HabonRoof/nixietube_clock/doc/picture/tap_inductor/IR/FLIR0199.jpg

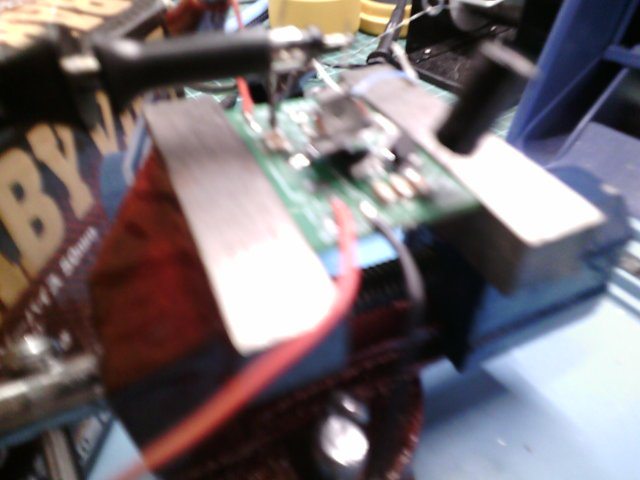
doc/picture/tap_inductor/IR/FLIR0199.jpg
