HabonRoof/nixietube_clock/doc/datasheet/divergence_meter_eevblog.gif

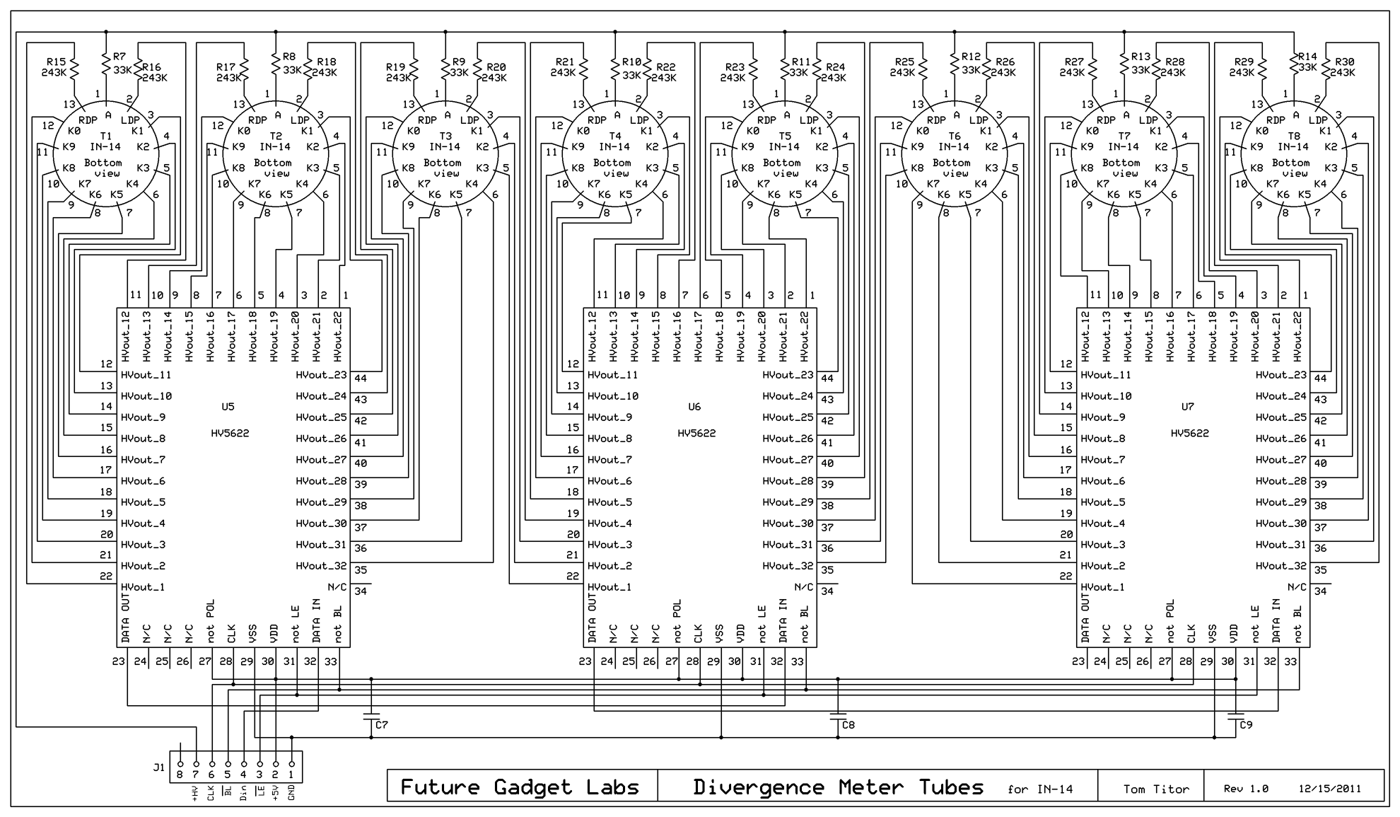
doc/datasheet/divergence_meter_eevblog.gif
