HabonRoof/nixietube_clock/doc/picture/single_board/IR/10mA_1.jpg

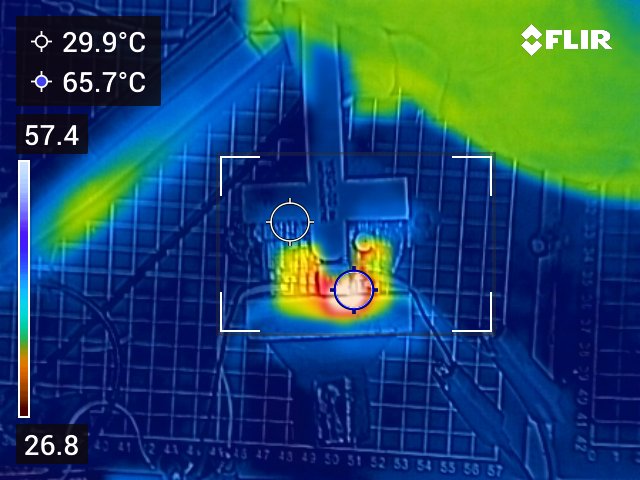
doc/picture/single_board/IR/10mA_1.jpg
