HabonRoof/nixietube_clock/doc/picture/single_board/IR/10mA_3.jpg

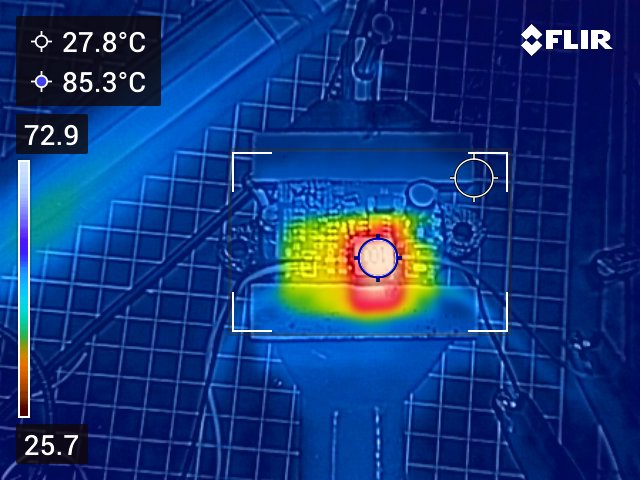
doc/picture/single_board/IR/10mA_3.jpg
