HabonRoof/nixietube_clock/doc/picture/single_board/waveform/0A175V000.png

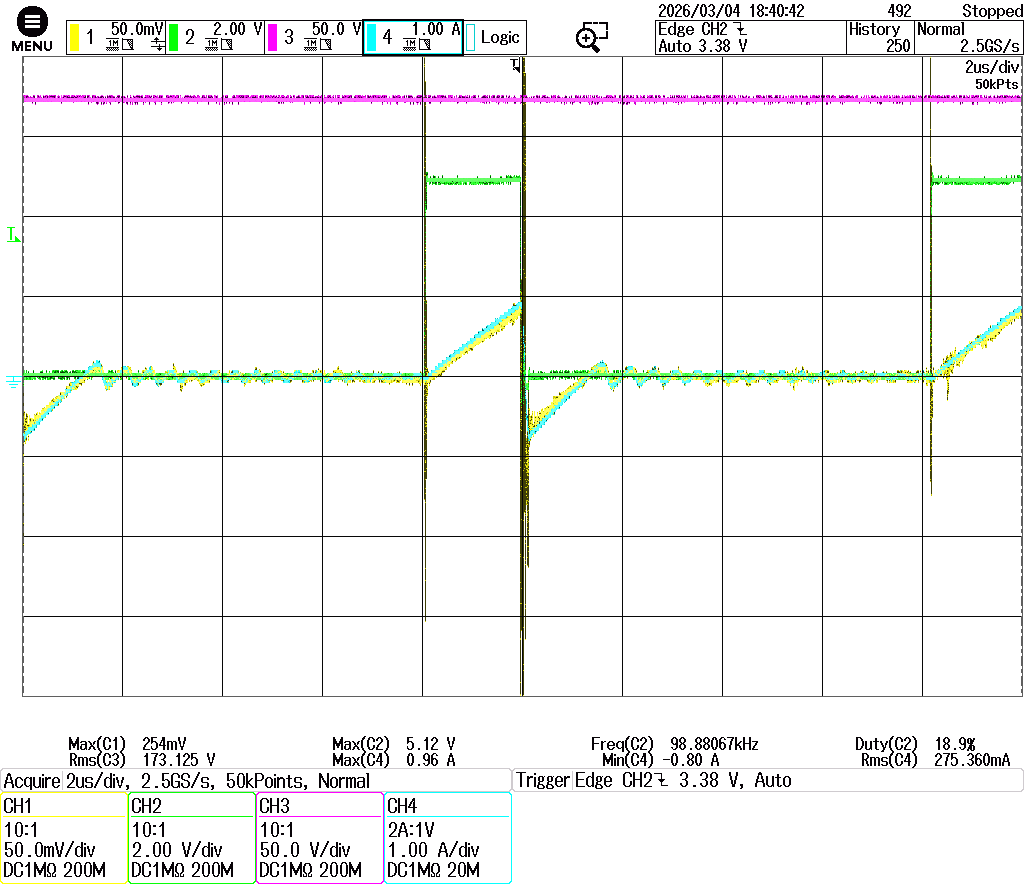
doc/picture/single_board/waveform/0A175V000.png
