HabonRoof/nixietube_clock/doc/picture/single_board/waveform/5vin_160vout_0Aout.png

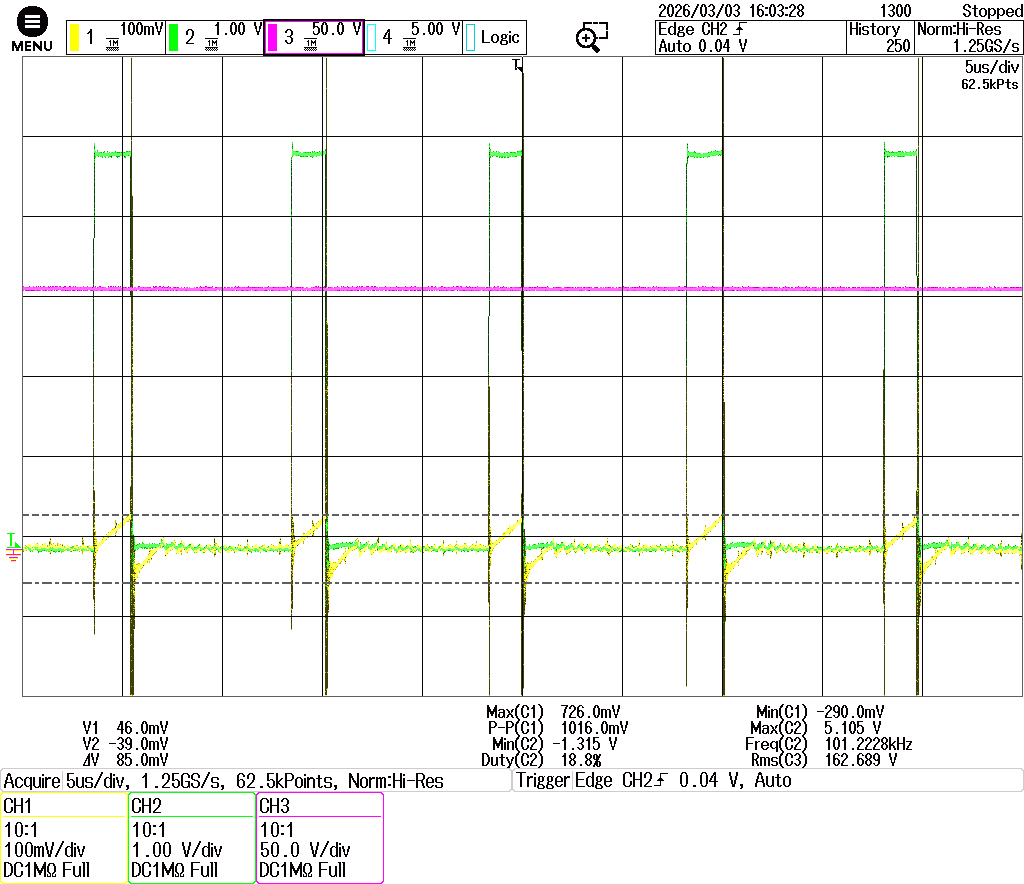
doc/picture/single_board/waveform/5vin_160vout_0Aout.png
