HabonRoof/nixietube_clock/doc/picture/single_board/waveform/5vin_160vout_5mAout.png

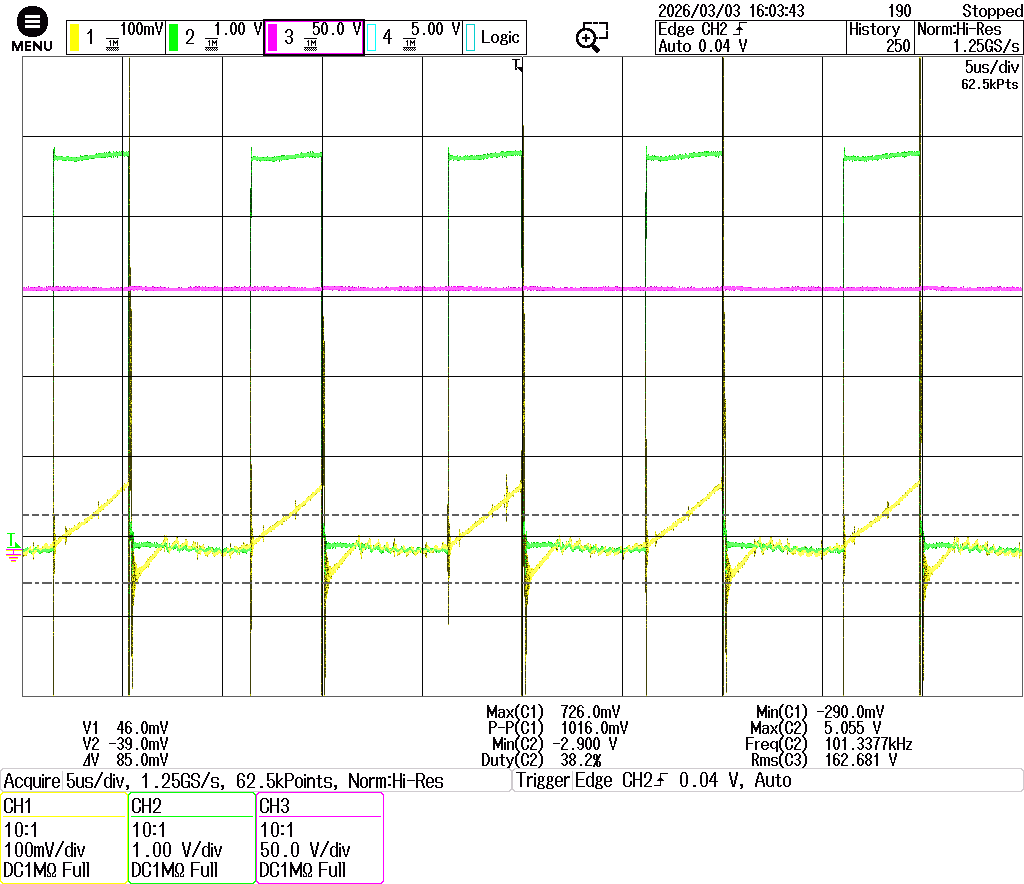
doc/picture/single_board/waveform/5vin_160vout_5mAout.png
