HabonRoof/nixietube_clock/doc/picture/single_board/waveform/8mA175V000.png

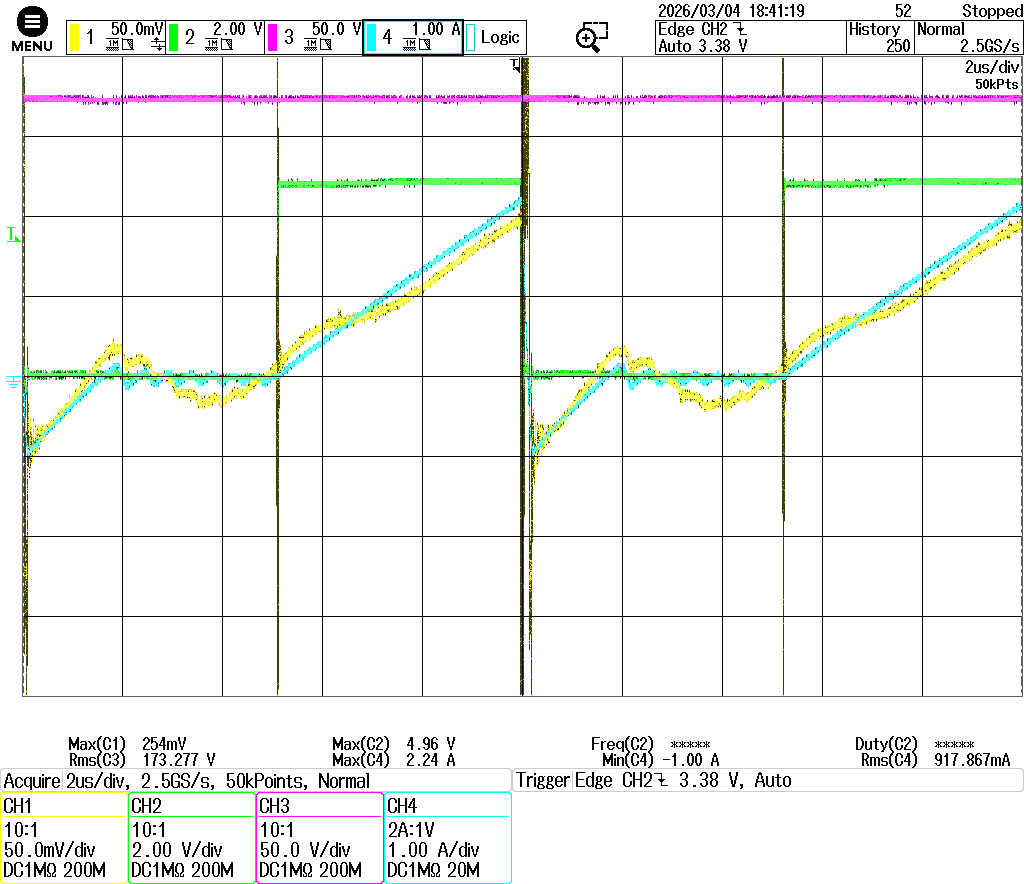
doc/picture/single_board/waveform/8mA175V000.png
