HabonRoof/nixietube_clock/doc/picture/single_board/waveform/175V0ARsen23p5000.png

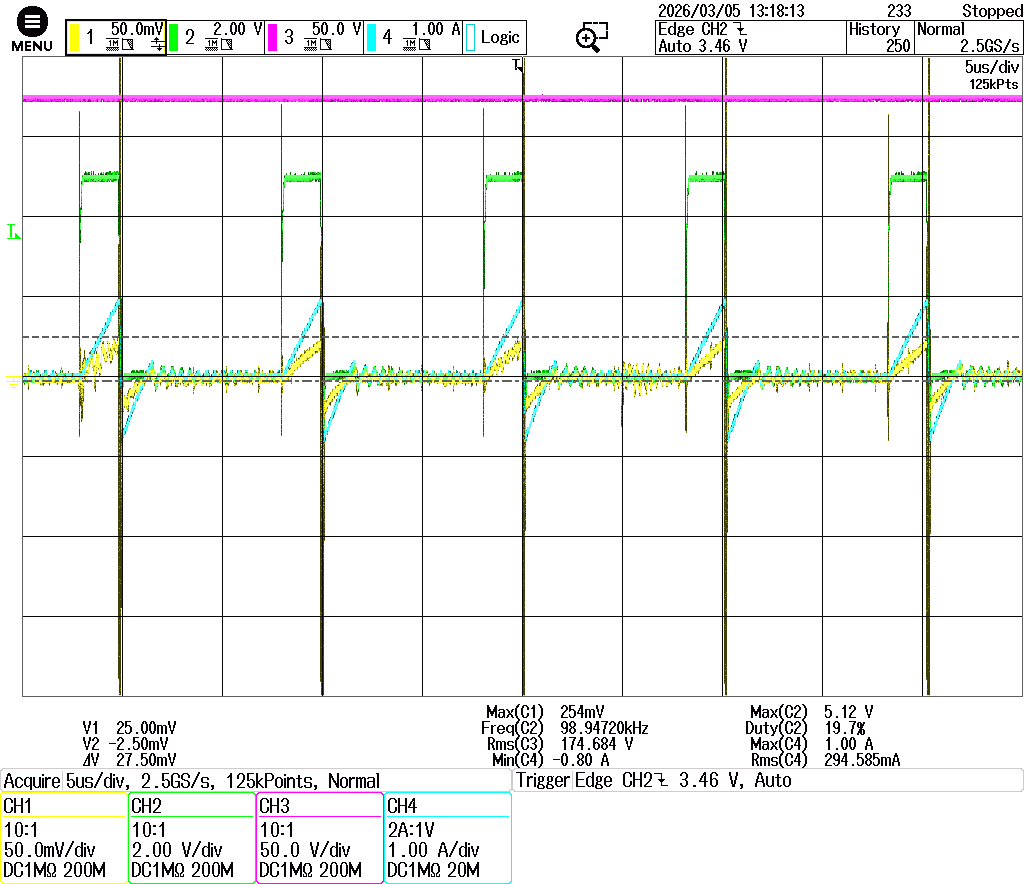
doc/picture/single_board/waveform/175V0ARsen23p5000.png
