HabonRoof/nixietube_clock/doc/picture/single_board/waveform/175V10mARsen23p5001.png

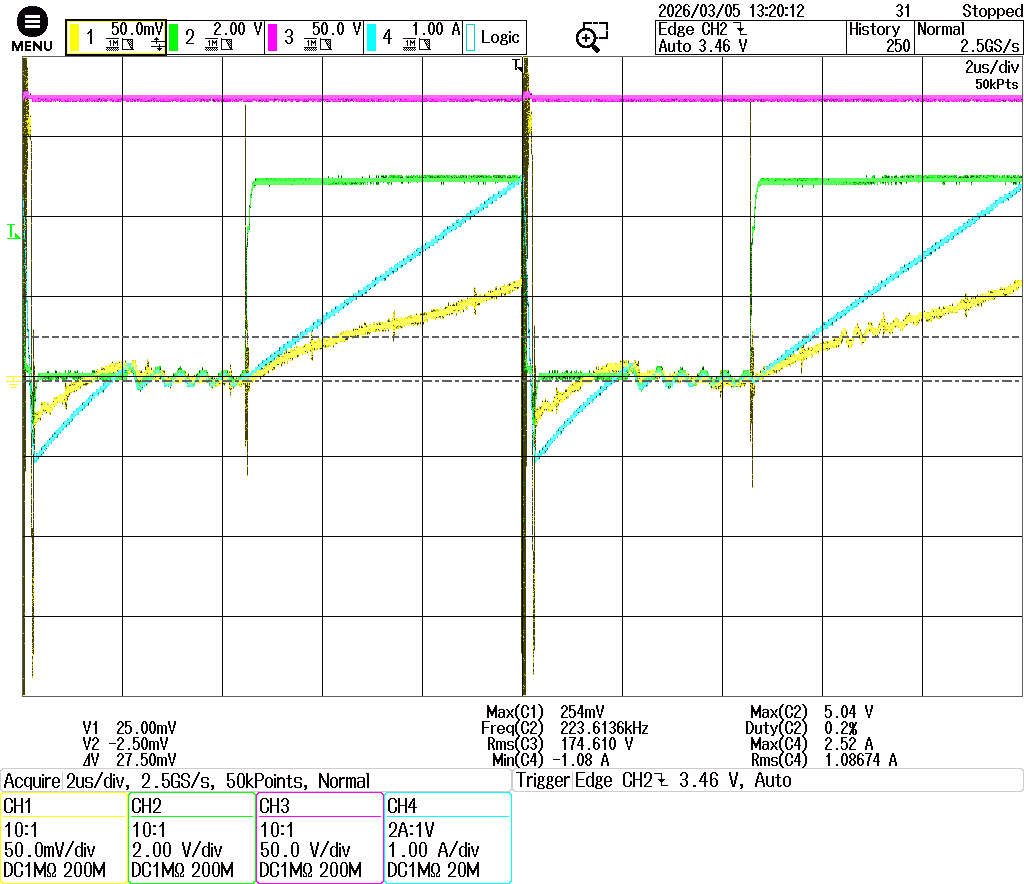
doc/picture/single_board/waveform/175V10mARsen23p5001.png
