HabonRoof/nixietube_clock/doc/picture/tap_inductor/155uH_N2/150V5mA001.png

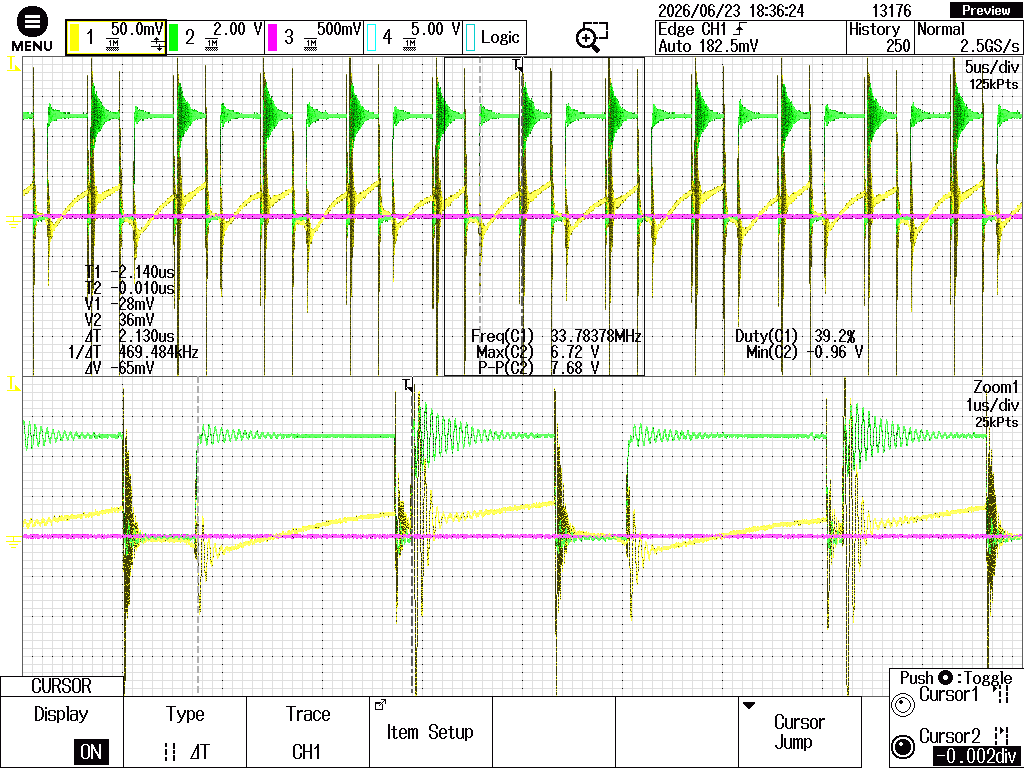
doc/picture/tap_inductor/155uH_N2/150V5mA001.png
