HabonRoof/nixietube_clock/doc/picture/tap_inductor/155uH_N2/172V3mA000.png

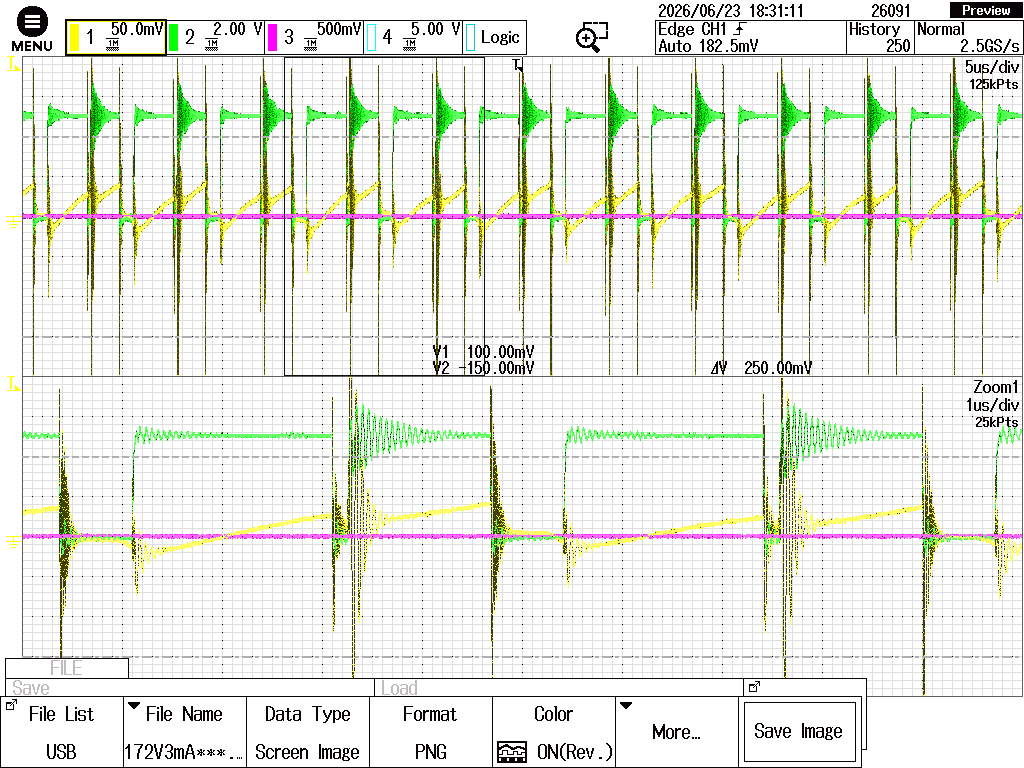
doc/picture/tap_inductor/155uH_N2/172V3mA000.png
