HabonRoof/nixietube_clock/doc/picture/tap_inductor/IR/FLIR0190.jpg

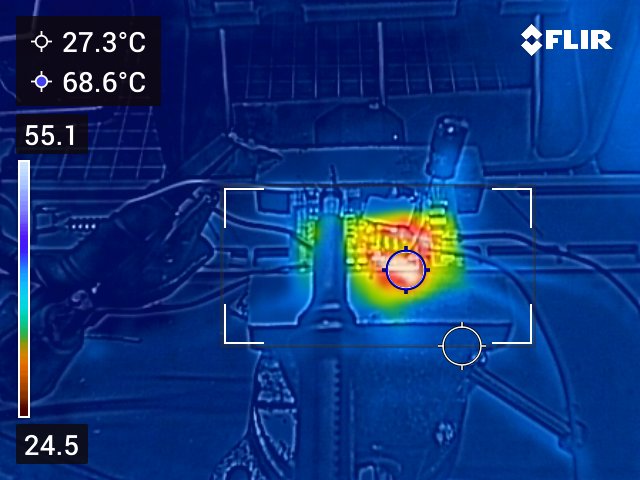
doc/picture/tap_inductor/IR/FLIR0190.jpg
