HabonRoof/nixietube_clock/doc/picture/tap_inductor/IR/FLIR0191.jpg

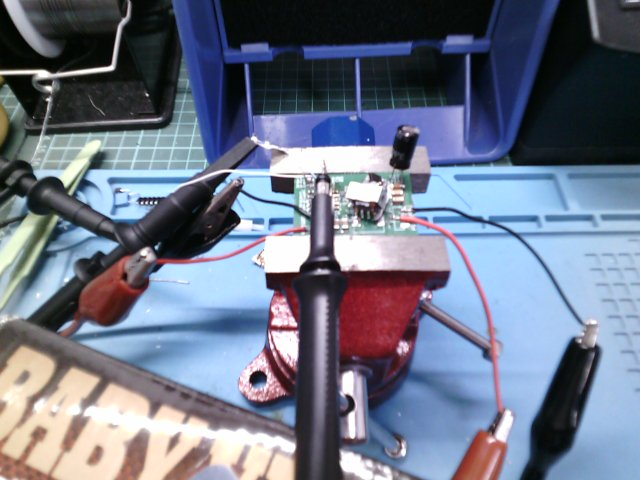
doc/picture/tap_inductor/IR/FLIR0191.jpg
