HabonRoof/nixietube_clock/doc/picture/tap_inductor/IR/FLIR0192.jpg

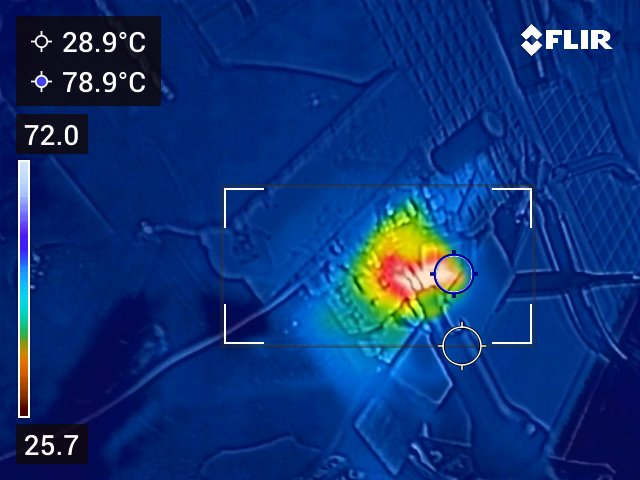
doc/picture/tap_inductor/IR/FLIR0192.jpg
