HabonRoof/nixietube_clock/doc/picture/tap_inductor/IR/FLIR0193.jpg

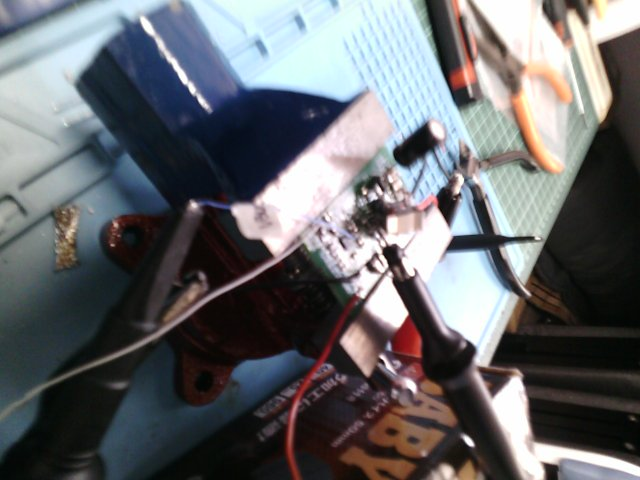
doc/picture/tap_inductor/IR/FLIR0193.jpg
