HabonRoof/nixietube_clock/doc/picture/tap_inductor/IR/FLIR0195.jpg

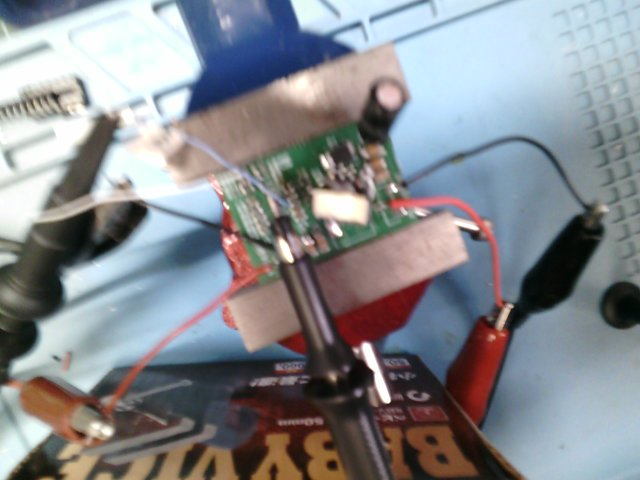
doc/picture/tap_inductor/IR/FLIR0195.jpg
