HabonRoof/nixietube_clock/doc/picture/tap_inductor/IR/FLIR0196.jpg

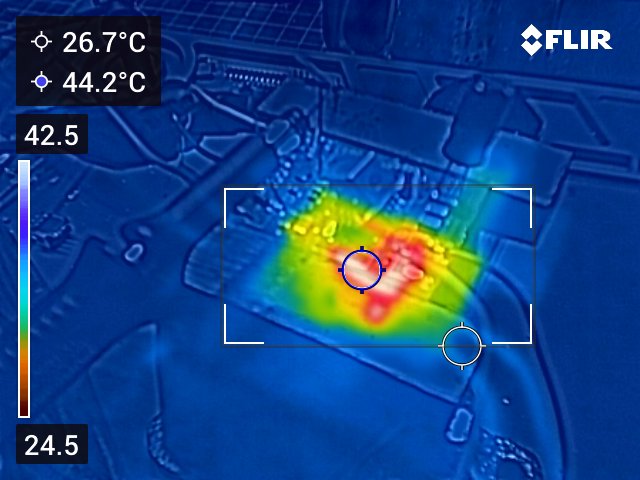
doc/picture/tap_inductor/IR/FLIR0196.jpg
