HabonRoof/nixietube_clock/doc/picture/tap_inductor/IR/FLIR0197.jpg

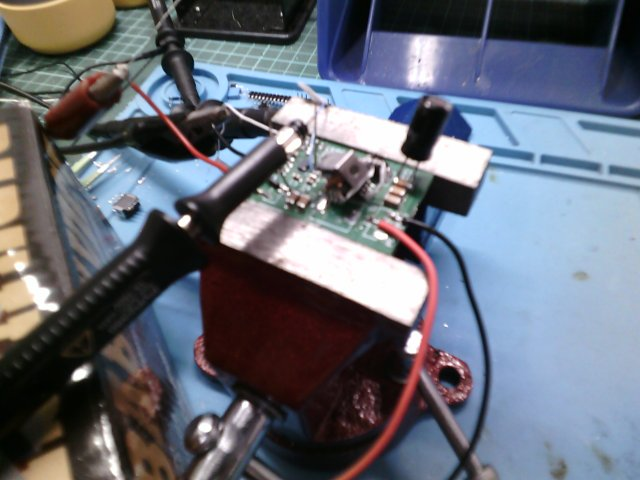
doc/picture/tap_inductor/IR/FLIR0197.jpg
