HabonRoof/nixietube_clock/doc/picture/tap_inductor/IR/FLIR0198.jpg

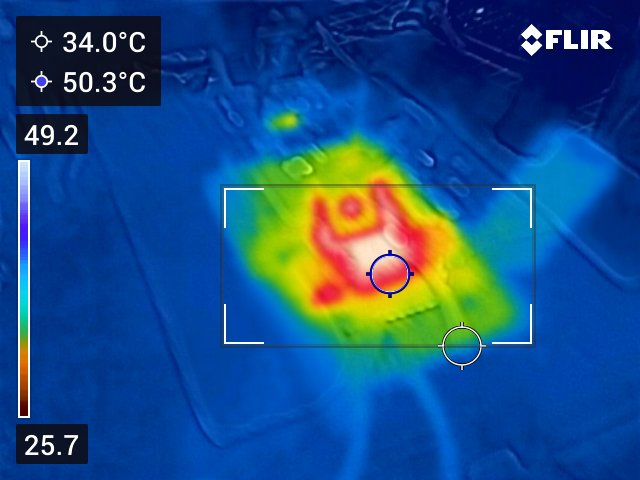
doc/picture/tap_inductor/IR/FLIR0198.jpg
