HabonRoof/nixietube_clock/src/audio_driver.cpp

#include "audio_driver.h"

AudioDriver::AudioDriver(uart_port_t uart_num)
    : player_(uart_num),
      initialized_(false)
{
}

void AudioDriver::ensure_initialized()
{
    if (!initialized_) {
        player_.begin();
        initialized_ = true;
    }
}

esp_err_t AudioDriver::play_from_mp3_folder(uint16_t file_number)
{
    ensure_initialized();
    return player_.play_from_mp3_folder(file_number);
}

esp_err_t AudioDriver::set_loop(bool enable)
{
    ensure_initialized();
    return player_.set_loop(enable);
}

esp_err_t AudioDriver::stop()
{
    ensure_initialized();
    return player_.stop();
}

esp_err_t AudioDriver::pause()
{
    ensure_initialized();
    return player_.pause();
}

esp_err_t AudioDriver::resume()
{
    ensure_initialized();
    return player_.resume();
}

esp_err_t AudioDriver::set_volume(uint8_t volume)
{
    ensure_initialized();
    return player_.set_volume(volume);
}

esp_err_t AudioDriver::volume_up()
{
    ensure_initialized();
    return player_.volume_up();
}

esp_err_t AudioDriver::volume_down()
{
    ensure_initialized();
    return player_.volume_down();
}

esp_err_t AudioDriver::play_next()
{
    ensure_initialized();
    return player_.play_next();
}

esp_err_t AudioDriver::play_previous()
{
    ensure_initialized();
    return player_.play_previous();
}

esp_err_t AudioDriver::query_sd_track_count(uint16_t *out_count, uint32_t timeout_ms)
{
    ensure_initialized();
    return player_.query_sd_track_count(out_count, timeout_ms);
}

esp_err_t AudioDriver::query_playback_status(DfPlayerPlaybackStatus *out_status, uint16_t *out_track,
                                             uint32_t timeout_ms)
{
    ensure_initialized();
    return player_.query_playback_status(out_status, out_track, timeout_ms);
}

esp_err_t AudioDriver::set_low_power_mode(bool enable)
{
    ensure_initialized();
    return player_.set_low_power_mode(enable);
}

AudioPlaybackState AudioDriver::state() const
{
    return player_.state();
}
