HabonRoof/nixietube_clock/src/color_model.cpp

#include "color_model.h"

#include <algorithm>
#include <cmath>

namespace
{
const uint8_t kGammaTable[256] = {
    0,   0,   0,   0,   0,   0,   0,   0,   0,   0,   0,   0,   0,   0,   0,   1,
    1,   1,   1,   1,   1,   1,   1,   1,   1,   2,   2,   2,   2,   2,   2,   2,
    3,   3,   3,   3,   3,   4,   4,   4,   4,   5,   5,   5,   5,   6,   6,   6,
    6,   7,   7,   7,   8,   8,   8,   9,   9,   9,  10,  10,  11,  11,  11,  12,
    12,  13,  13,  13,  14,  14,  15,  15,  16,  16,  17,  17,  18,  18,  19,  19,
    20,  20,  21,  22,  22,  23,  23,  24,  25,  25,  26,  26,  27,  28,  28,  29,
    30,  30,  31,  32,  33,  33,  34,  35,  35,  36,  37,  38,  39,  39,  40,  41,
    42,  43,  43,  44,  45,  46,  47,  48,  49,  49,  50,  51,  52,  53,  54,  55,
    56,  57,  58,  59,  60,  61,  62,  63,  64,  65,  66,  67,  68,  69,  70,  71,
    73,  74,  75,  76,  77,  78,  79,  81,  82,  83,  84,  85,  87,  88,  89,  90,
    91,  93,  94,  95,  97,  98,  99, 100, 102, 103, 105, 106, 107, 109, 110, 111,
   113, 114, 116, 117, 119, 120, 121, 123, 124, 126, 127, 129, 130, 132, 133, 135,
   137, 138, 140, 141, 143, 145, 146, 148, 149, 151, 153, 154, 156, 158, 159, 161,
   163, 165, 166, 168, 170, 172, 173, 175, 177, 179, 181, 182, 184, 186, 188, 190,
   192, 194, 196, 197, 199, 201, 203, 205, 207, 209, 211, 213, 215, 217, 219, 221,
   223, 225, 227, 229, 231, 234, 236, 238, 240, 242, 244, 246, 248, 251, 253, 255,
};
} // namespace

RgbColor hsv_to_rgb(const HsvColor &hsv)
{
    float hue = static_cast<float>(hsv.hue % 360);
    float saturation = static_cast<float>(hsv.saturation) / 255.0f;
    float value = static_cast<float>(hsv.value) / 255.0f;

    float chroma = value * saturation;
    float hue_section = hue / 60.0f;
    float x = chroma * (1.0f - std::fabs(std::fmod(hue_section, 2.0f) - 1.0f));

    float r1 = 0.0f;
    float g1 = 0.0f;
    float b1 = 0.0f;

    if (hue_section >= 0.0f && hue_section < 1.0f)
    {
        r1 = chroma;
        g1 = x;
    }
    else if (hue_section >= 1.0f && hue_section < 2.0f)
    {
        r1 = x;
        g1 = chroma;
    }
    else if (hue_section >= 2.0f && hue_section < 3.0f)
    {
        g1 = chroma;
        b1 = x;
    }
    else if (hue_section >= 3.0f && hue_section < 4.0f)
    {
        g1 = x;
        b1 = chroma;
    }
    else if (hue_section >= 4.0f && hue_section < 5.0f)
    {
        r1 = x;
        b1 = chroma;
    }
    else
    {
        r1 = chroma;
        b1 = x;
    }

    float match = value - chroma;
    uint8_t red = static_cast<uint8_t>(std::round((r1 + match) * 255.0f));
    uint8_t green = static_cast<uint8_t>(std::round((g1 + match) * 255.0f));
    uint8_t blue = static_cast<uint8_t>(std::round((b1 + match) * 255.0f));

    return RgbColor{red, green, blue};
}

HsvColor rgb_to_hsv(const RgbColor &rgb)
{
    float r = static_cast<float>(rgb.red) / 255.0f;
    float g = static_cast<float>(rgb.green) / 255.0f;
    float b = static_cast<float>(rgb.blue) / 255.0f;

    float max_val = std::max({r, g, b});
    float min_val = std::min({r, g, b});
    float delta = max_val - min_val;

    float h = 0.0f;
    float s = 0.0f;
    float v = max_val;

    if (delta > 0.0f)
    {
        s = delta / max_val;

        if (max_val == r)
        {
            h = (g - b) / delta;
        }
        else if (max_val == g)
        {
            h = 2.0f + (b - r) / delta;
        }
        else
        {
            h = 4.0f + (r - g) / delta;
        }

        h *= 60.0f;
        if (h < 0.0f)
        {
            h += 360.0f;
        }
    }

    return HsvColor{
        static_cast<uint16_t>(std::round(h)),
        static_cast<uint8_t>(std::round(s * 255.0f)),
        static_cast<uint8_t>(std::round(v * 255.0f))};
}

RgbColor apply_gamma(const RgbColor &linear_color)
{
    RgbColor corrected{};
    corrected.red = kGammaTable[linear_color.red];
    corrected.green = kGammaTable[linear_color.green];
    corrected.blue = kGammaTable[linear_color.blue];
    return corrected;
}
